dmachtey/domotics/pictures/3d/3d_boards_model2.png

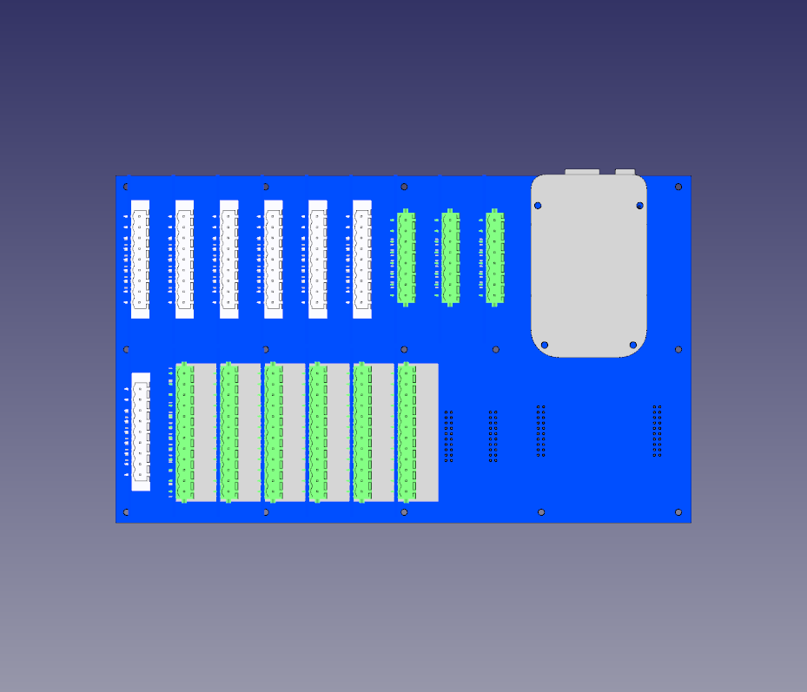
pictures/3d/3d_boards_model2.png
