dmachtey/domotics/pictures/main_bard_plus_out_board4.jpg

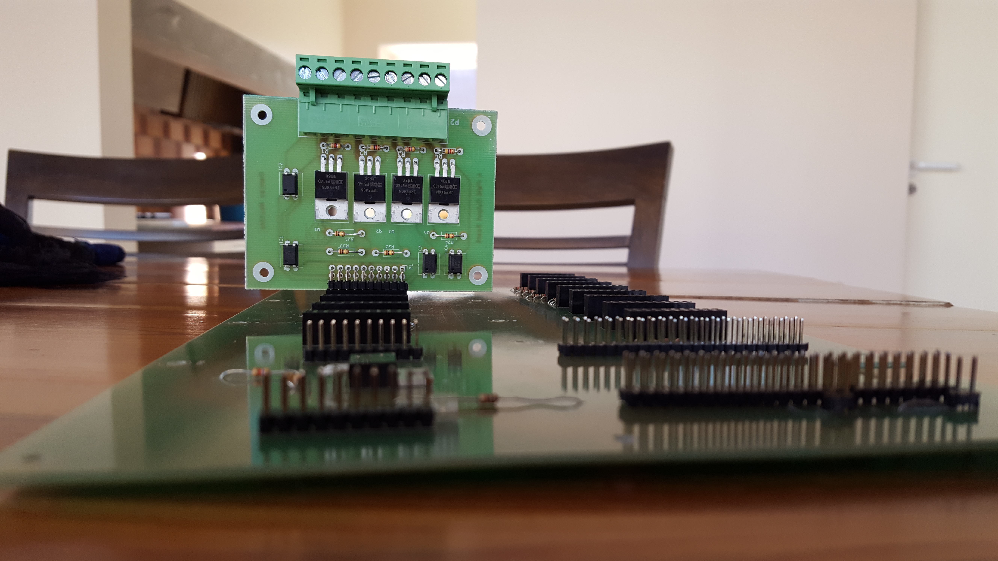
pictures/main_bard_plus_out_board4.jpg
