dmachtey/domotics/pictures/main_board.jpg

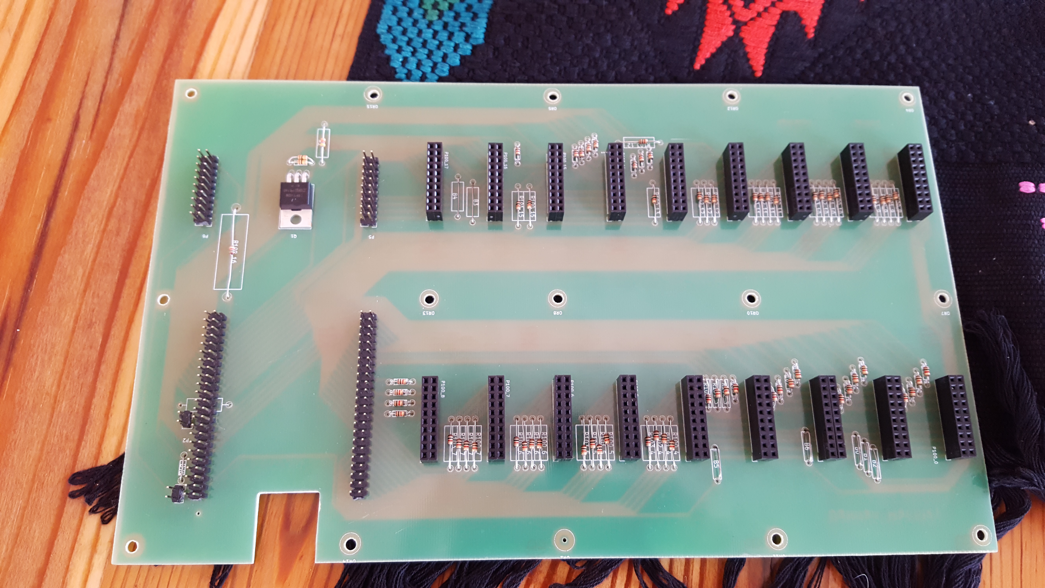
pictures/main_board.jpg
