dmachtey/domotics/pictures/main_board_back.jpg

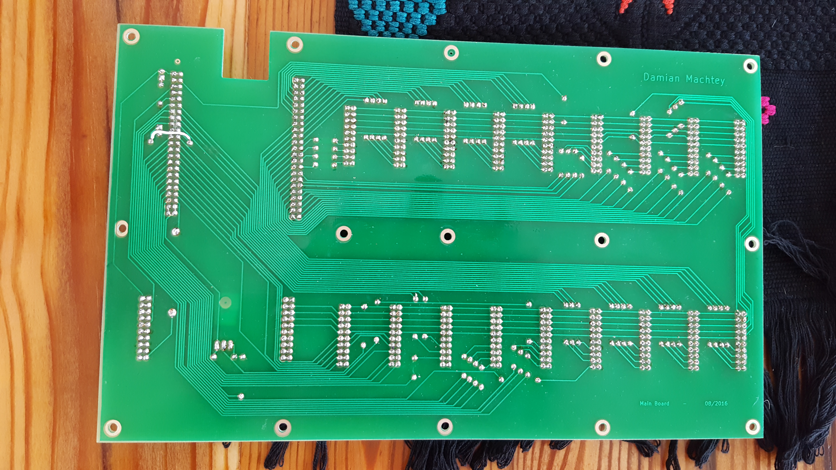
pictures/main_board_back.jpg
