dmachtey/domotics/src/pru_loader.cpp

// Filename: pru_loader.cpp
//
// Description:
// Author: Damian Machtey
// Maintainer:
//
// Created: Fri Aug  5 19:44:08 2016 (-0500)
//
// Last-Updated: Fri Jun 30 17:14:02 2017 (-0300)
//           By: Damian Machtey
//     Update #: 66

// Change Log:
//
//
// Copyright (C) 2016 Damian Machtey
//
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
//

// Code:
#include "pru_loader.h"

namespace lighting{

  PRULOADER::PRULOADER(std::string prubinary, pru_num pru){
    prunum = pru;
    if(getuid()!=0){
      std::cerr << "Error on PRULOADER. You must run this program as root. Exiting,,,"
                << std::endl;
      exit(EXIT_FAILURE);
    }

    // Initialize structure used by prussdrv_pruintc_intc
    // PRUSS_INTC_INITDATA is found in pruss_intc_mapping.h
    tpruss_intc_initdata pruss_intc_initdata = PRUSS_INTC_INITDATA;


    // Allocate and initialize memory
    prussdrv_init ();
    prussdrv_open(PRU_EVTOUT_0);

    // Map PRU's INTC
    prussdrv_pruintc_init(&pruss_intc_initdata);


    // place the samples in memory
    if (pru == zero)
      prussdrv_map_prumem(PRUSS0_PRU0_DATARAM, &pruDataMemory);
    else
      prussdrv_map_prumem(PRUSS0_PRU1_DATARAM, &pruDataMemory);


    pruDataMemory_int = (unsigned int *) pruDataMemory;


    // just in case, clear the exchange memory
    for (int r = 0; r<(64); r++){
      *(pruDataMemory_int+r) = 0;
      *(pruDataMemory_int+(0x100/4)+r) = 0;
    }
    D("memory cleared\n");

    // Load and execute binary on PRU
    if (prussdrv_exec_program (pru, prubinary.c_str())){
      std::cerr << "\nError on PRULOADER: Pru file not loaded " << std::endl;
      exit(EXIT_FAILURE);
    }
  }


  void PRULOADER::set_pwm(uint gpio, uint pwm){
    uint local_pwm = pwm;
    if (pwm < 0 ) local_pwm = 0;
    if (pwm > LOOPCOUNTER) local_pwm = LOOPCOUNTER;
    *(pruDataMemory_int+(gpio/4)) = local_pwm;
  }

  void PRULOADER::print(){
    for (int i=0; i<64; i++){
      std::cout << i << "  ";
      std::cout << *(pruDataMemory_int+(i)) << " << ";
      std::cout << *(pruDataMemory_int+((0x100/4)+i)) << std::endl;
    }
  }

  PRULOADER::~PRULOADER(){
      prussdrv_pru_disable(prunum);
      //prussdrv_exit ();
  }

} // namespace
//
// pru_loader.cpp ends here
