dmachtey/domotics/src/temperature.cpp

// Filename: temperature.cpp
//
// Description:
// Author: Damian Machtey
// Maintainer:
//
// Created: 2015-06-22 Mon
//
// Last-Updated: Wed Aug 10 08:34:13 2016 (-0500)
//           By: Damian Machtey
//     Update #: 39

// Change Log:
//
//
// Copyright (C) 2016 Damian Machtey
//
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
//

// Code:


#include <iostream>
#include <fstream>
#include <cstring>
#include <errno.h> // for errno

#include "temperature.h"

namespace lighting{

  TEMPERATURE::TEMPERATURE(std::string id, std::string host, int port,
                           std::string filename, uint publish_every_ms) :
    mosquittopp((const char *)id.c_str()){

    int keepalive = 60;
    connect(host.c_str(), port, keepalive);

    time_at = publish_every_ms;
    first_cycle = 0;
    mqtt_name = id;
    topic = id + "/send/temp";
    location = filename;
  }


  void TEMPERATURE::looop(unsigned int last_loop_ms){
    if (!first_cycle){
      time_ac = rand()%time_at;
      read();
      publish_now();
      first_cycle = 1;
    }
    time_ac += last_loop_ms;
    if (time_ac >= time_at){
      read();
      publish_now();
      time_ac = 0;
    }
    if(loop(15,1)){
      reconnect();
    }
  }


  void TEMPERATURE::read(){
    std::ifstream inFile(location.c_str(), std::ifstream::in);
    if (inFile.is_open()){
      getline(inFile, temp);
      inFile.close();
      temp = std::to_string(stof(temp)/1000.0f);
    }
    else {
      std::cerr << "Error on TEMPERATURE::read(): " << strerror(errno) << std::endl;
    }
  }


  void TEMPERATURE::publish_now(){
    publish(NULL, topic.c_str(), temp.length() , temp.c_str());
    D(topic << " Said temperature is: " << temp << std::endl;)
  }


  void TEMPERATURE::on_connect(int rc){
    std::cout << "Connected with code "  <<  rc << " from: TEMPERATURE::" << mqtt_name << std::endl;
  }


  void TEMPERATURE::on_message(const struct mosquitto_message *message){
    std::cout << "no messages allowed" << std::endl;
  }


  void TEMPERATURE::on_subscribe(int mid, int qos_count, const int *granted_qos){
    std::cout << topic << " Subscription succeeded" << std::endl;
  }

  TEMPERATURE::~TEMPERATURE(){
    std::cout << "destroying TEMPERATURE::" << mqtt_name << std::endl;
  }
} /* namespace lighting */

//
// temperature.cpp ends here
