dmachtey/domotics/pictures/main_bard_plus_out_board3.jpg

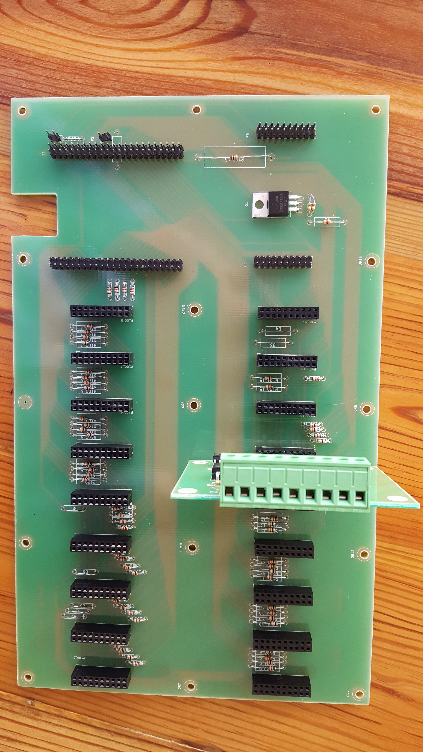
pictures/main_bard_plus_out_board3.jpg
