dmachtey/domotics/pictures/out_board.jpg

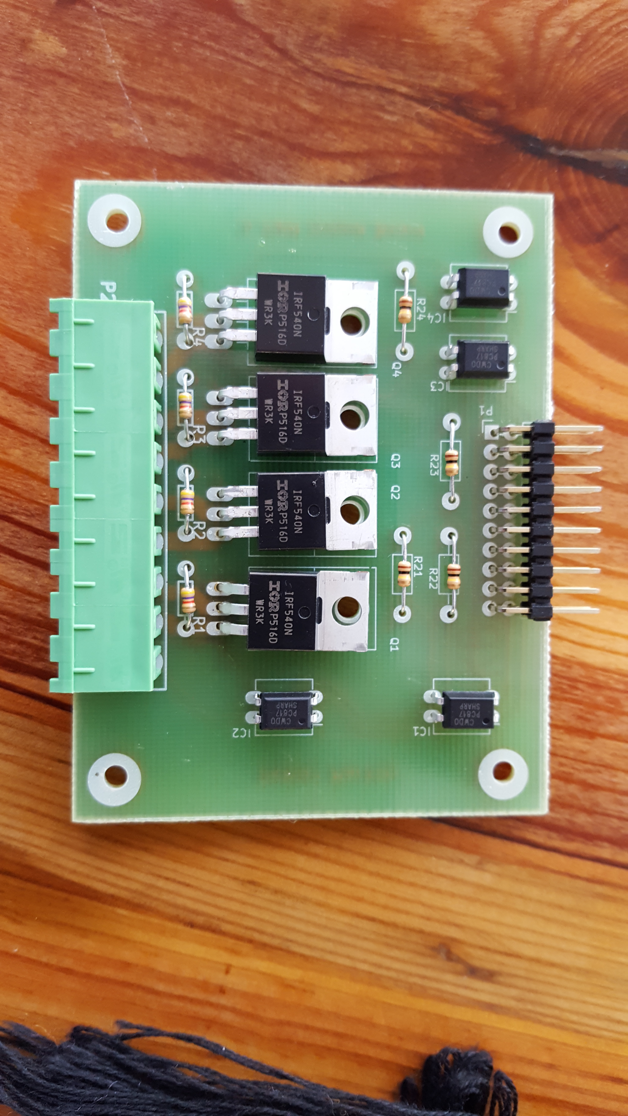
pictures/out_board.jpg
